nathangarciaf/AutomaticGardenSprinkler/esquemático/circuito/circuito.kicad_sch

## KiCad design esquemático/circuito/circuito.kicad_sch (2025-09-01, an earlier design)

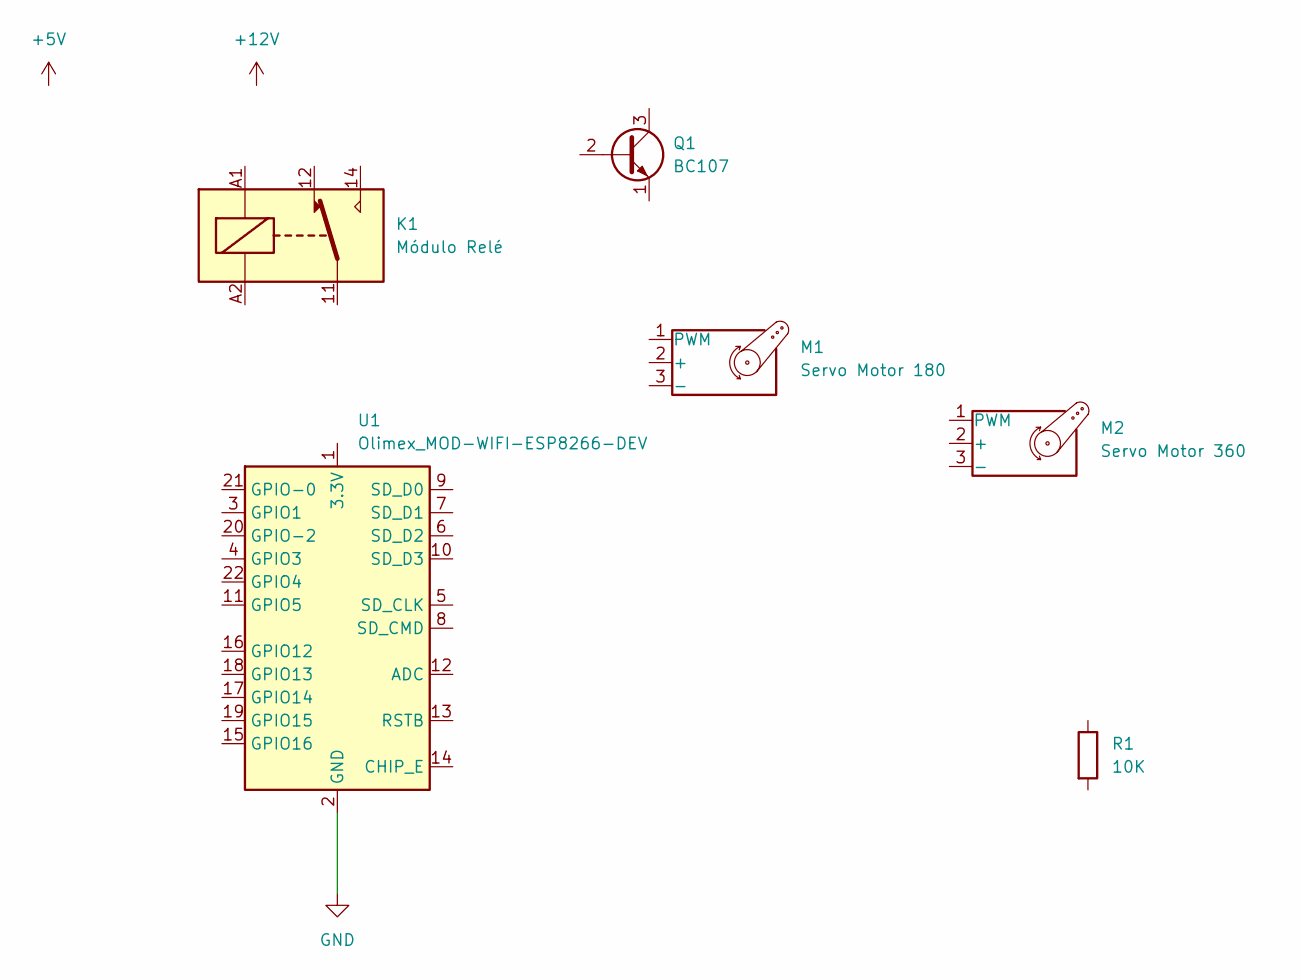
[picture p8: schematic circuito.kicad_sch]

Parts:
K1: Módulo Relé; Relay_SPDT_Fujitsu_FTR-LYCA005x_FormC_Vertical
M1: Servo Motor 180
M2: Servo Motor 360
Q1: BC107; TO-18-3
R1: 10K
U1: Olimex_MOD-WIFI-ESP8266-DEV

Connections:
GND: U1.2 (GND)
